KENASTES/Circuit_LED_cube_8x8x8_Project/Docs/Project_Image/66044027-F697-4E45-84AF-40B526537A3A.jpg

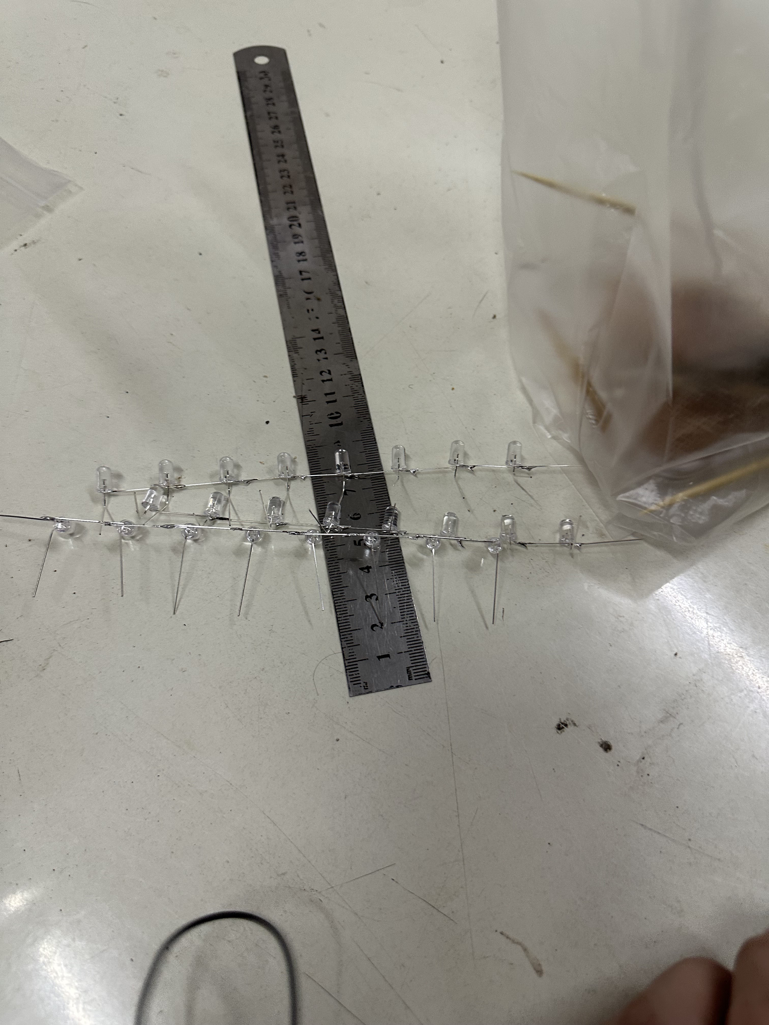
Docs/Project_Image/66044027-F697-4E45-84AF-40B526537A3A.jpg
