KENASTES/Circuit_LED_cube_8x8x8_Project/Docs/Project_Image/IMG_20250301_010001.jpg

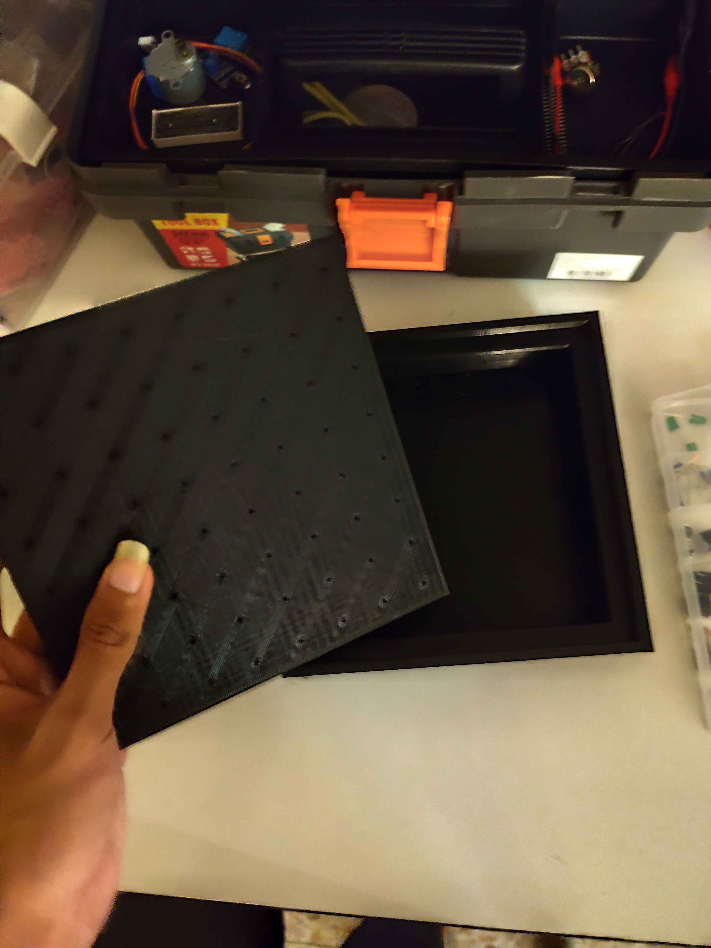
Docs/Project_Image/IMG_20250301_010001.jpg
