KENASTES/Circuit_LED_cube_8x8x8_Project/Docs/Project_Image/IMG_20250304_180110.jpg

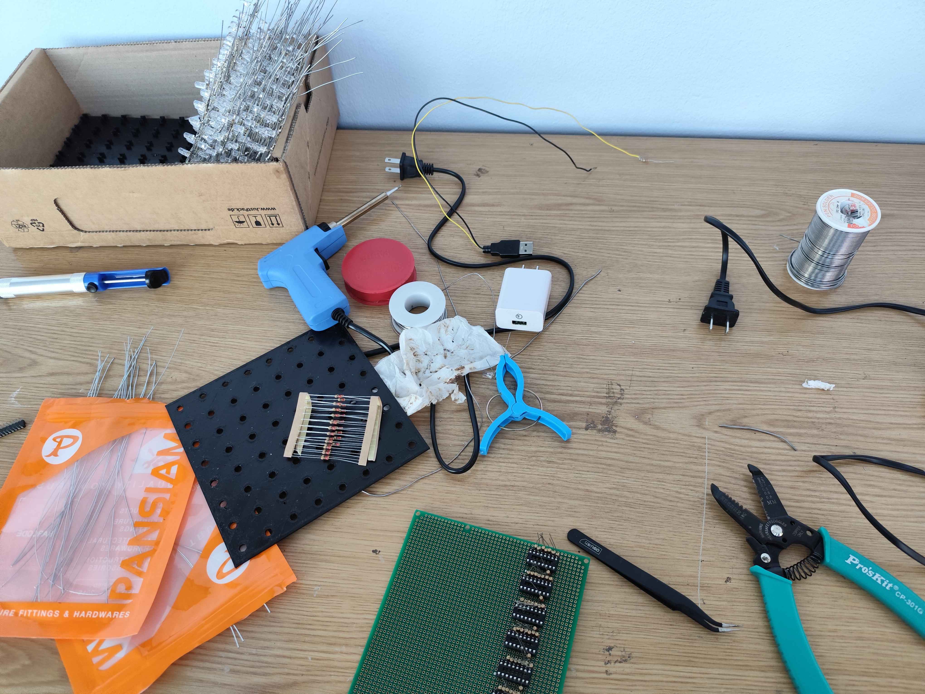
Docs/Project_Image/IMG_20250304_180110.jpg
