KENASTES/Circuit_LED_cube_8x8x8_Project/Docs/Project_Image/IMG_20250323_153621.jpg

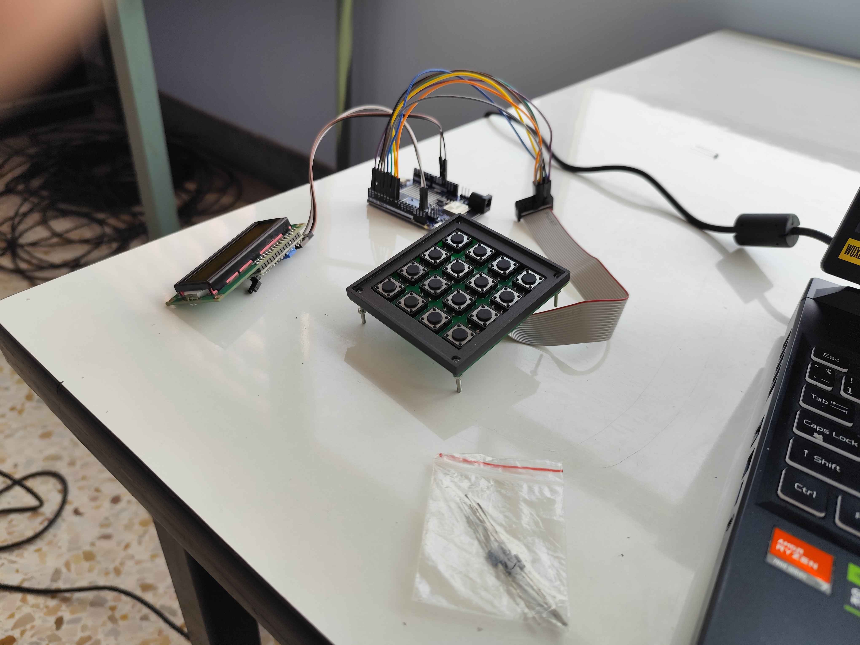
Docs/Project_Image/IMG_20250323_153621.jpg
