KENASTES/Circuit_LED_cube_8x8x8_Project/Docs/Project_Image/CD4814EF-942F-4DC3-A8B8-CCC03DC483A6.jpg

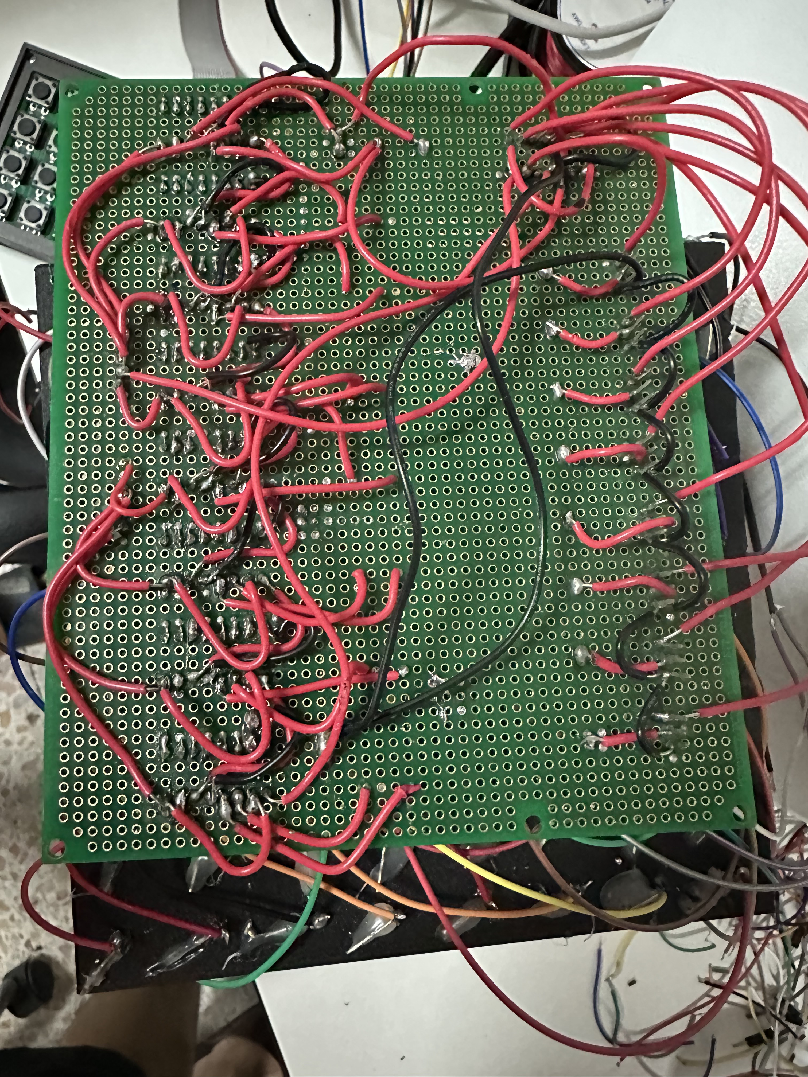
Docs/Project_Image/CD4814EF-942F-4DC3-A8B8-CCC03DC483A6.jpg
